reluxa/temp-monitor/casing/solidworks/assembled_parts_screen_2.png

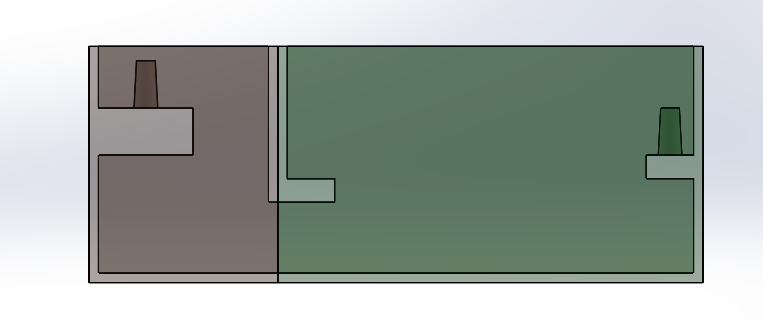
casing/solidworks/assembled_parts_screen_2.png
