reluxa/temp-monitor/casing/solidworks/assembled_part_scren.png

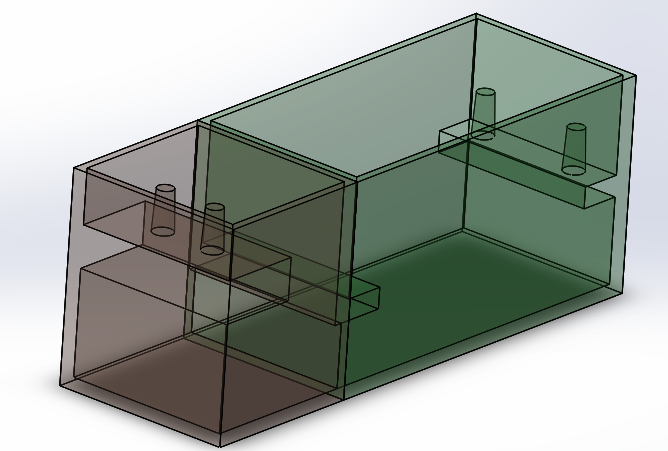
casing/solidworks/assembled_part_scren.png
